Romano047/Electroencefalograma-AD620/Simulación/EEG_2nd_Design.cir

[Main]
FileType=CIR
Version=12.00
Program=Micro-Cap
Component Version=10.00
Shape Version=11.00
Screen=1366,768
MCAPVersion=12.2.0.5
Key ID=Demo
NLCnt=248
TXCnt=40

[shapedef]
Name=Battery
Line=0,0,22,0
Line=22,-3,22,3
Line=26,-7,26,7
Line=26,0,48,0
Current=32,8,16,8

[shapedef]
Name=Capacitor
Line=0,0,22,0
Line=22,-8,22,8
Line=26,-8,26,8
Line=26,0,48,0
Current=32,12,16,12

[shapedef]
Name=Diode
Root="Diode.root",0,0,0

[shapedef]
Name=Diode.root
Line=0,0,20,0
Line=28,0,48,0
Rectangle=18,-8,20,8
PolyClosed=3
PolyLine=20,0
PolyLine=28,-8
PolyLine=28,8
Current=32,16,16,16

[shapedef]
Name=Ground
Line=0,0,12,0
Line=12,-8,12,8
Line=18,-4,18,4
Line=24,0,24,0

[shapedef]
Name=Minus.root
Line=-2,0,2,0

[shapedef]
Name=Opamp5
Root="Opamp.root",0,0,0
Root="Plus.root",25,-4,0
Root="Minus.root",25,52,0
Line=32,56,32,34
Line=32,-8,32,13

[shapedef]
Name=Opamp8_RG_In
Root="Plus.root",14,2,0
Root="Minus.root",14,46,0
Line=0,0,8,0
Line=0,48,8,48
Line=8,-8,8,56
Line=8,56,72,24
Line=8,-8,72,24
Line=24,48,24,64
Root="Plus.root",18,-15,0
Root="Minus.root",18,62,0
Line=24,0,24,-16
Line=72,24,88,24
Line=56,32,56,48
Line=0,16,8,16
Line=0,32,8,32

[shapedef]
Name=Opamp.root
Line=0,48,6,48
Line=0,0,5,0
Line=6,-4,6,52
Line=6,-4,48,24
Line=6,52,48,24
Line=48,24,72,24
Line=10,12,14,12
Line=12,10,12,14
Line=10,36,14,36
Line=4,0,6,0

[shapedef]
Name=Plus.root
Line=-2,0,2,0
Line=0,-2,0,2

[shapedef]
Name=Pot
Line=0,0,12,0
Line=12,0,14,-4
Line=14,-4,18,4
Line=18,4,22,-4
Line=22,-4,26,4
Line=26,4,30,-4
Line=30,-4,34,4
Line=34,4,36,0
Line=36,0,48,0
PolyClosed=4
PolyLine=24,4
PolyLine=24,4
PolyLine=22,8
PolyLine=26,8
Line=24,8,24,16

[shapedef]
Name=Resistor
PolyOpen=12
PolyLine=0,0
PolyLine=0,0
PolyLine=12,0
PolyLine=14,-4
PolyLine=18,4
PolyLine=22,-4
PolyLine=26,4
PolyLine=30,-4
PolyLine=34,4
PolyLine=36,0
PolyLine=48,0
PolyLine=48,0
Current=32,8,16,8

[shapedef]
Name=SPICE_V
Root="Vsource.root",0,0,0

[shapedef]
Name=Vsource.root
Line=0,0,12,0
Line=36,0,48,0
Ellipse=12,-12,36,12
FColor=None
Line=7,5,7,9
Root="Plus.root",41,7,0
Current=32,16,16,16

[compdef]
Name=Opamp
Definition=Opamp
Shape=Opamp5
Mask=5121
Used=84
memo=Opamp
Label Offset=44,29,-14,39
PinCnt=5
Pin="Plus input",0,0,-31,-7
Pin="Minus input",0,6,-33,20
Pin="VEE",4,7,3,-5
Pin="Output",9,3,-13,-4
Pin="VCC",4,-1,5,14

[compdef]
Name=Battery
Definition=Battery
Shape=Battery
Mask=7425
Used=128
memo=Battery
Label Offset=19,7,10,13
PinCnt=2
Pin="Plus",6,0,-4,-5
Pin="Minus",0,0,-10,-5

[compdef]
Name=Ground
Definition=Ground
Shape=Ground
Mask=257
Used=517
memo=Ground
Label Offset=0,0,0,0
PinCnt=1
Pin="PinA",0,0,-3,-7

[compdef]
Name=Diode
Definition=Diode
Shape=Diode
Mask=4353
Used=25
memo=Diode
Label Offset=17,10,12,12
PinCnt=2
Pin="Anode",6,0,-9,-8
Pin="Cathode",0,0,-20,-8

[compdef]
Name=AD620_AD
Definition=Subckt
Shape=Opamp8_RG_In
Mask=4224
Used=4
memo=Low Power Instrumentation Amplifier
Label Offset=69,33,-8,46
PinCnt=8
Pin="7",a,0,2,-2,0
Pin="2",a,0,6,-2,0
Pin="1",a,0,0,-2,-1
Pin="50",a,3,8,5,8
Pin="20",a,7,6,5,8
Pin="46",a,11,3,-5,-1
Pin="99",a,3,-2,5,7
Pin="8",a,0,4,-2,0

[compdef]
Name=Resistor
Definition=Resistor
Shape=Resistor
Mask=6145
Used=494
memo=Resistor
Label Offset=18,6,8,11
PinCnt=2
Pin="Plus",6,0,-10,-4
Pin="Minus",0,0,-14,-4

[compdef]
Name=Capacitor
Definition=Capacitor
Shape=Capacitor
Mask=6145
Used=93
memo=Capacitor
Label Offset=16,12,12,12
PinCnt=2
Pin="Plus",6,0,-3,-5
Pin="Minus",0,0,-14,-5

[compdef]
Name=Voltage Source
Definition=VSpice
Shape=SPICE_V
Mask=5377
Used=130
memo=Voltage Source
Label Offset=19,13,15,13
PinCnt=2
Pin="Plus",6,0,-5,-6
Pin="Minus",0,0,-20,-6

[compdef]
Name=Pot
Definition=Macro
Shape=Pot
Mask=4096
Used=17
memo=Potentiometer Macro
Label Offset=32,4,9,11
PinCnt=3
Pin="PINA",a,0,0,-13,-5
Pin="PINB",a,3,2,6,5
Pin="PINC",a,6,0,-12,-5

[Circuit]
Window Placement=2,3, -1,-1, -8,-31, 78,78,1083,394
Default Object=Color=#000080
Default Object Font=Height=-15,FStyle=0,Color=#000080,Name=Arial
Default Object Apply Border To Text=No
Default Object Apply Fill To Text=No
Default Object GridSnap=No
NodeVoltageFormat=3
CurrentFormat=3
PowerFormat=3
PathDelayFormat=3
WarningFormat=3
GridTextFormulaFormat=3
Window Placement in Transient Analysis=2,3, -1,-1, -8,-31, 94,152,1295,468
Window Placement in AC Analysis=2,3, -1,-1, -8,-31, 130,130,1331,446
Window Placement in DC Analysis=2,3, -1,-1, -8,-31, 52,52,1253,368
SpiceType=AMBIGUOUS
Title_Block_Border=None
Title_Block=False
Show Nodes=False
Show Voltages=True
Show Current=False
Show Power=False
Show Condition=False
Show Pin Connections=False
Show Connection Warnings=False
Show Cross=False
Show Attribute Text=True
Show Grid Text=True

[Comp]
Name=Opamp
Px=752,320
Rot=4

[Attr]
ON=44,-43,PART
V=X1
Style=8192

[Attr]
ON=44,-57,MODEL
V=lm358

[Attr]
ON=44,-85,PACKAGE
V=TO-5C_8

[Comp]
Name=Battery
Px=48,80
Rot=3
Page=3

[Attr]
ON=-24,9,PART
V=V1
Style=8192

[Attr]
ON=-24,25,VALUE
V=5
Style=8192

[Comp]
Name=Ground
Px=48,80
Rot=7
Page=3

[Comp]
Name=Battery
Px=112,32
Rot=1
Page=3

[Attr]
ON=15,57,PART
V=V2
Style=8192

[Attr]
ON=16,72,VALUE
V=5
Style=8192

[Comp]
Name=Ground
Px=112,80
Rot=7
Page=3

[Comp]
Name=Opamp
Px=752,496
Rot=4

[Attr]
ON=44,-43,PART
V=X2
Style=8192

[Attr]
ON=44,-57,MODEL
V=lm358

[Attr]
ON=44,-85,PACKAGE
V=TO-5C_8

[Attr]
ON=44,-99,GATE
V=A

[Attr]
ON=44,-113,COMPNAME
V=UX2

[Wire]
Pxs=728,272,752,272

[Wire]
Pxs=728,232,728,272

[Wire]
Pxs=728,232,824,232

[Wire]
Pxs=824,232,824,296

[Wire]
Pxs=728,448,752,448

[Wire]
Pxs=728,416,728,448

[Wire]
Pxs=728,416,824,416

[Wire]
Pxs=824,416,824,472

[Wire]
Pxs=624,320,696,320

[Wire]
Pxs=624,496,696,496

[Comp]
Name=Diode
Px=696,496
Rot=1

[Attr]
ON=12,12,PART
V=D1
Style=8192

[Attr]
ON=12,26,MODEL
V=1N456

[Attr]
ON=12,54,PACKAGE
V=DO-35

[Wire]
Pxs=696,496,752,496

[Comp]
Name=Diode
Px=696,448
Rot=1

[Attr]
ON=12,12,PART
V=D2
Style=8192

[Attr]
ON=12,26,MODEL
V=1N456

[Attr]
ON=12,54,PACKAGE
V=DO-35

[Comp]
Name=Diode
Px=696,320
Rot=1

[Attr]
ON=12,12,PART
V=D3
Style=8192

[Attr]
ON=12,26,MODEL
V=1N456

[Attr]
ON=12,54,PACKAGE
V=DO-35

[Wire]
Pxs=696,320,752,320

[Comp]
Name=Diode
Px=696,272
Rot=1

[Attr]
ON=12,12,PART
V=D4
Style=8192

[Attr]
ON=12,26,MODEL
V=1N456

[Attr]
ON=12,54,PACKAGE
V=DO-35

[Comp]
Name=AD620_AD
Px=984,360

[Attr]
ON=69,33,PART
V=X3
Style=8192

[Attr]
ON=69,47,NAME
V=AD620_AD

[Attr]
ON=69,75,PACKAGE
V=DIP8

[Comp]
Name=Resistor
Px=936,360
Rot=1

[Attr]
ON=8,11,PART
V=R1
Style=8192

[Attr]
ON=7,24,RESISTANCE
V=56
Style=8192

[Attr]
ON=0,0,PACKAGE
V

[Wire]
Pxs=968,376,984,376

[Wire]
Pxs=968,360,968,376

[Wire]
Pxs=936,360,968,360

[Wire]
Pxs=968,392,984,392

[Wire]
Pxs=968,392,968,408

[Wire]
Pxs=824,296,872,296

[Wire]
Pxs=984,296,984,360

[Comp]
Name=Capacitor
Px=1088,384

[Attr]
ON=16,12,PART
V=C1
Style=8192

[Attr]
ON=16,26,CAPACITANCE
V=470u
Style=8192

[Attr]
ON=0,0,PACKAGE
V

[Comp]
Name=Resistor
Px=1152,400
Rot=1

[Attr]
ON=8,11,PART
V=R4
Style=8192

[Attr]
ON=8,25,RESISTANCE
V=680
Style=8192

[Attr]
ON=0,0,PACKAGE
V

[Wire]
Pxs=1136,384,1152,384

[Wire]
Pxs=1152,384,1152,400

[Wire]
Pxs=1152,384,1192,384

[Comp]
Name=Ground
Px=1152,464
Rot=1

[Wire]
Pxs=1152,448,1152,464

[Wire]
Pxs=1072,384,1088,384

[Comp]
Name=Voltage Source
Px=624,432
Rot=5

[Attr]
ON=15,-27,PART
V=V3
Style=8192

[Attr]
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
CBorder=None

[Grid Text]
Text="DRL_IN"
Px=776,384
GridSnap=True
JustifyH=Left
JustifyV=Bottom
CBorder=None

[Grid Text]
Text="Vout"
Px=2384,408
GridSnap=True
JustifyH=Left
JustifyV=Bottom
CBorder=None

[Grid Text]
Text="Vin"
Px=624,320
GridSnap=True
JustifyH=Left
JustifyV=Bottom
CBorder=None

[Grid Text]
Text="-V"
Px=1008,424
GridSnap=True
JustifyH=Left
JustifyV=Bottom
CBorder=None

[Grid Text]
Text="+V"
Px=1008,344
GridSnap=True
JustifyH=Left
JustifyV=Bottom
CBorder=None

[Grid Text]
Text="-V"
Px=696,544
GridSnap=True
JustifyH=Left
JustifyV=Bottom
CBorder=None

[Grid Text]
Text="+V"
Px=696,448
GridSnap=True
JustifyH=Left
JustifyV=Bottom
CBorder=None

[Grid Text]
Text="-V"
Px=696,368
GridSnap=True
JustifyH=Left
JustifyV=Bottom
CBorder=None

[Grid Text]
Text="+V"
Px=696,272
GridSnap=True
JustifyH=Left
JustifyV=Bottom
CBorder=None

[Grid Text]
Text="+V"
Px=48,32
GridSnap=True
JustifyH=Left
JustifyV=Bottom
Page=3
CBorder=None

[Grid Text]
Text="+V"
Px=784,328
GridSnap=True
JustifyH=Left
JustifyV=Bottom
CBorder=None

[Grid Text]
Text="-V"
Px=112,32
GridSnap=True
JustifyH=Left
JustifyV=Bottom
Page=3
CBorder=None

[Grid Text]
Text="-V"
Px=784,264
GridSnap=True
JustifyH=Left
JustifyV=Bottom
CBorder=None

[Grid Text]
Text="+V"
Px=784,504
GridSnap=True
JustifyH=Left
JustifyV=Bottom
CBorder=None

[Grid Text]
Text="-V"
Px=784,440
GridSnap=True
JustifyH=Left
JustifyV=Bottom
CBorder=None

[Grid Text]
Text="+V"
Px=1352,440
GridSnap=True
JustifyH=Left
JustifyV=Bottom
CBorder=None

[Grid Text]
Text="-V"
Px=1352,376
GridSnap=True
JustifyH=Left
JustifyV=Bottom
CBorder=None

[Grid Text]
Text="+V"
Px=1584,416
GridSnap=True
JustifyH=Left
JustifyV=Bottom
CBorder=None

[Grid Text]
Text="-V"
Px=1584,352
GridSnap=True
JustifyH=Left
JustifyV=Bottom
CBorder=None

[Grid Text]
Text="+V"
Px=1608,472
GridSnap=True
JustifyH=Left
JustifyV=Bottom
CBorder=None

[Grid Text]
Text="-V"
Px=1608,536
GridSnap=True
JustifyH=Left
JustifyV=Bottom
CBorder=None

[Grid Text]
Text="+V"
Px=1912,440
GridSnap=True
JustifyH=Left
JustifyV=Bottom
CBorder=None

[Grid Text]
Text="-V"
Px=1912,376
GridSnap=True
JustifyH=Left
JustifyV=Bottom
CBorder=None

[Grid Text]
Text="+V"
Px=2104,464
GridSnap=True
JustifyH=Left
JustifyV=Bottom
CBorder=None

[Grid Text]
Text="-V"
Px=2104,400
GridSnap=True
JustifyH=Left
JustifyV=Bottom
CBorder=None

[Grid Text]
Text="VC"
Px=192,32
GridSnap=True
JustifyH=Left
JustifyV=Bottom
Page=3
CBorder=None

[Grid Text]
Text="VE"
Px=256,32
GridSnap=True
JustifyH=Left
JustifyV=Bottom
Page=3
CBorder=None

[Grid Text]
Text="VC"
Px=320,32
GridSnap=True
JustifyH=Left
JustifyV=Bottom
Page=3
CBorder=None

[Grid Text]
Text="+V"
Px=2304,440
GridSnap=True
JustifyH=Left
JustifyV=Bottom
CBorder=None

[Grid Text]
Text="VE"
Px=384,32
GridSnap=True
JustifyH=Left
JustifyV=Bottom
Page=3
CBorder=None

[Grid Text]
Text="VC1"
Px=448,32
GridSnap=True
JustifyH=Left
JustifyV=Bottom
Page=3
CBorder=None

[Grid Text]
Text="+V"
Px=728,808
GridSnap=True
JustifyH=Left
JustifyV=Bottom
CBorder=None

[Grid Text]
Text="VE1"
Px=512,32
GridSnap=True
JustifyH=Left
JustifyV=Bottom
Page=3
CBorder=None

[Grid Text]
Text="-V"
Px=728,744
GridSnap=True
JustifyH=Left
JustifyV=Bottom
CBorder=None

[Grid Text]
Text="+V"
Px=912,832
GridSnap=True
JustifyH=Left
JustifyV=Bottom
CBorder=None

[Grid Text]
Text="-V"
Px=912,768
GridSnap=True
JustifyH=Left
JustifyV=Bottom
CBorder=None

[Grid Text]
Text="-V"
Px=1160,848
GridSnap=True
JustifyH=Left
JustifyV=Bottom
CBorder=None

[Grid Text]
Text="+V"
Px=1160,752
GridSnap=True
JustifyH=Left
JustifyV=Bottom
CBorder=None

[Schematic]
CurrentSection 0=0
CurrentSection 1=0
CurrentSection 2=0
CurrentSection 3=0
Splitter.xs=0
Splitter.ys=0
TextQuad=4099
Scale=1.3333333333333333
GridUser=10
ShapeGroups="Main","Euro","Polarity","Main1","Main11","Electrolytic","GroundArrow","DeMorgan"
CalcRMS=False
CalcAVG=False
CalcPeak=False
CalcVoltage=True
DisplayMeasure=Last
ShareScales=True

[Tools]
Pos=Top
FILESAVEASOLD=No
BOM=No
FILEPCB=No
PROBE=Yes
SELECT=Yes
PAN=Yes
COMP=Yes
TEXT=Yes
WIRE=Yes
WIRED=Yes
BUS=Yes
GRAPHIC=Yes
FLOWCHART=Yes
LINE=No
ELLIPSE=No
RECT=No
DIAM=No
ARC=No
PIE=No
TRIANGLE=No
STAR=No
LEFTBRK=No
RIGHTBRK=No
BOTHBRK=No
META=No
PARALLELOGRAM=No
FC_PROCESS=No
FC_ALT_PROCESS=No
FC_DECISION=No
FC_DATA=No
FC_PREDEFPROCESS=No
FC_INTERNALSTORAGE=No
FC_DOCUMENT=No
FC_MULTIDOCUMENT=No
FC_TERMINATOR=No
FC_PREPARATION=No
FC_MANUALINPUT=No
FC_MANUALOPERATION=No
FC_CONNECTOR=No
FC_OFFPAGECONNECTOR=No
FC_PUNCHCARD=No
FC_PUNCHEDTAPE=No
FC_SUMMING_JUNCTION=No
FC_OR=No
FC_COLLATE=No
FC_SORT=No
FC_EXTRACT=No
FC_MERGE=No
FC_STORED_DATA=No
FC_DELAY=No
FC_SAS=No
FC_MAGNETIC_DISK=No
FC_DAS=No
FC_DISPLAY=No
SPREAD_SHEET=Yes
POLYCLOS=No
POLYOPEN=No
FLAG=Yes
INFO=Yes
HELP=Yes
HELP_SPICE=No
LINK=Yes
CHECK=Yes
REGION_ENABLE=Yes
TITLE_BLOCK=Yes
DIGTRC=No
DIGTRC2=No
BUILD_COMMAND=Yes
DIGALL=No
GRIDTEXT=Yes
COMPTEXT=Yes
NODE=Yes
MEASURED=Yes
NODEV=Yes
CURRENT=Yes
POWER=Yes
CONDITIN=Yes
PIN=Yes
CONNWARN=Yes
CROSS=No
GRID=Yes
BORDER=Yes
BORDERONE=Yes
TITLE=Yes
RUBBER=Yes
PROPERTY=Yes
STEP=Yes
MIRROR=Yes
ROTATE=Yes
FLIPY=Yes
FLIPX=Yes
CIR_MAKEMACRO=No
CLEARCUTWIRE=No
CLIPBOARDCIRPAGE2BMM=No
FINDCOMP=Yes
FIND=Yes
REPEAT=No
REPLACE=No
MODEL=Yes
CIR2CKT=No
ATTDISP=No
ENABLE=Yes
DISABLE=Yes
ENABLE_WITH=Yes
TOFRONT=Yes
TOBACK=Yes
SELNEXT=No
PAGEADD=No
PAGEADDTEXT=No
ADDSECTION=No
PAGEDEL=No
ZOOMIN=Yes
ZOOMOUT=Yes
AUTOSCALECIR=Yes
GOTOFLAG=No
UPLEVEL=Yes
COLOR=Yes
FONT=Yes
STYLE=Yes
DM_LAST=No
DM_RMS=No
DM_AVG=No
DM_PEAK=No
GRID_NONE=No
GRID_NORMAL=No
GRID_BOLD_5=No
GRID_BOLD_6=No
GRID_BOLD_USER=No
GRAPH_PAPER=No
SPLITCIRTEXTH=No
SPLITCIRTEXTV=No
SPACE_SPLITTERS_EVENLY=No
NORMALCIR=No
RENAMEDEFINE=No
RENAMECMP=No
ATTALIGN=No
RESETNODEPOS=No
FIT2STANDARD=No
NODESNAP=No
MOVETEXT=No
TEXTINC=No
TOGGLETEXT=No
TOGGLEMODE=No
TOLERANCE=No
ALIGNAB=No
ALIGNLEFT=No
ALIGNCENTER=No
ALIGNRIGHT=No
ALIGNTOP=No
ALIGNMIDDLES=No
ALIGNBOTTOM=No

[Section]
Index=0
Name="EEG_2nd_Design"
Type=Main
Enable=True
CurrentPage 0=0
CurrentPage 1=0
CurrentPage 2=0
CurrentPage 3=0
TabSize 0=425
TabSize 1=425
TabSize 2=425
TabSize 3=425

[Page]
Index=0
Section=0
Print=True
Enable=True
Name=Main
PrinterScale=1
Scale 0=1
Scale 1=1
Scale 2=1
SB 3=699,218
Scale 3=1.3333333333333333
Px=824,382
WinBackGround Color=#FFFFFF
Select Color=#FF0000
Anchor Color=#000000
Select Box Color=#000080
Grid Text Color=Height=-12,FStyle=0,Color=#0000FF,Name=Verdana
Grid Text RTF=False
Grid Text Angle=0
Grid Text GridSnap=True
Grid Text PinIt=False
Grid Text JustifyH=Left
Grid Text JustifyV=Bottom
Grid GradientColor2=None
Grid OutlineThickness=1
Grid OutlineColor=None
Component Color=#0000FF
Attribute Text=Height=-12,FStyle=0,Color=#008000,Name=Verdana
Wire Color=#008000
Bus Color=#008000
Pin Connection=Height=-10,FStyle=0,Color=#FF0000,Name=Arial
Pin Marker Color=#008000
Node Number=Height=-11,FStyle=0,Color=#FF00FF,Name=Arial
Node Voltage Color=Height=-11,FStyle=0,Color=#000000,Name=Arial
Dynamic AC Voltage Color=#E4E4E4
Text Banner Text=Height=-15,FStyle=0,Color=#800000,Name=Arial
Title Block Background=#C0C0C0
Current=Height=-11,FStyle=0,Color=#0000FF,Name=Arial
Power/Condition=Height=-11,FStyle=0,Color=#FF0000,Name=Arial
Digital Path Color=#FF0000
Title Block Border=#000000
Disabled	Color=#C0C0C0
Search Color=#FFFF00
Grid Color=#000000
Graph Paper=#E4E4E4
Digital 0 Color=#000000
Digital R Color=#FFFF00
Digital F Color=#FFFF00
Digital 1 Color=#FF0000
Digital X Color=#C0C0C0
Digital Z Color=#808080
Block Select Color=#51F998

[Page]
Index=1
Section=0
Type=Text
Print=False
Enable=True
Name=Text
Font=Height=-15,FStyle=0,Color=#000000,Name=Courier New
Comment Color=#008000
WinBackGround Color=#FFFFFF
Disabled	Color=#C0C0C0
KeyWord Color=#0000FF
Error	Color=#FF0000
Search Color=#FFFF00

[Page]
Index=2
Section=0
Type=Text
Print=False
Enable=True
Name=Models
Font=Height=-15,FStyle=0,Color=#000000,Name=Courier New
Comment Color=#008000
WinBackGround Color=#FFFFFF
Disabled	Color=#C0C0C0
KeyWord Color=#0000FF
Error	Color=#FF0000
Search Color=#FFFF00

[Page]
Index=3
Section=0
Print=True
Enable=True
Name=Power Supplies
PrinterScale=1
Scale 0=1
Scale 1=1
Scale 2=1
Scale 3=0.66666666666666663
Px=218,178
WinBackGround Color=#FFFFFF
Select Color=#FF0000
Anchor Color=#000000
Select Box Color=#000080
Grid Text Color=Height=-12,FStyle=0,Color=#0000FF,Name=Verdana
Grid Text RTF=False
Grid Text Angle=0
Grid Text GridSnap=True
Grid Text PinIt=False
Grid Text JustifyH=Left
Grid Text JustifyV=Bottom
Grid GradientColor2=None
Grid OutlineThickness=1
Grid OutlineColor=None
Component Color=#0000FF
Attribute Text=Height=-12,FStyle=0,Color=#008000,Name=Verdana
Wire Color=#008000
Bus Color=#008000
Pin Connection=Height=-10,FStyle=0,Color=#FF0000,Name=Arial
Pin Marker Color=#008000
Node Number=Height=-11,FStyle=0,Color=#FF00FF,Name=Arial
Node Voltage Color=Height=-11,FStyle=0,Color=#000000,Name=Arial
Dynamic AC Voltage Color=#E4E4E4
Text Banner Text=Height=-15,FStyle=0,Color=#800000,Name=Arial
Title Block Background=#C0C0C0
Current=Height=-11,FStyle=0,Color=#0000FF,Name=Arial
Power/Condition=Height=-11,FStyle=0,Color=#FF0000,Name=Arial
Digital Path Color=#FF0000
Title Block Border=#000000
Disabled	Color=#C0C0C0
Search Color=#FFFF00
Grid Color=#000000
Graph Paper=#E4E4E4
Digital 0 Color=#000000
Digital R Color=#FFFF00
Digital F Color=#FFFF00
Digital 1 Color=#FF0000
Digital X Color=#C0C0C0
Digital Z Color=#808080
Block Select Color=#51F998

[Page]
Index=4
Section=0
Type=Info
Print=False
Enable=True
Name=Info
Font=Height=-15,FStyle=0,Color=#000000,Name=Courier New
Comment Color=#008000
WinBackGround Color=#FFFFFF
Disabled	Color=#C0C0C0
KeyWord Color=#0000FF
Error	Color=#FF0000
Search Color=#FFFF00

[Text Area]
Section=0
Page=1
Text=.OPTIONS ITL4=50
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
